yuskegoto/BluetoothDongleForTing/tingCode/OiDs/15001.png

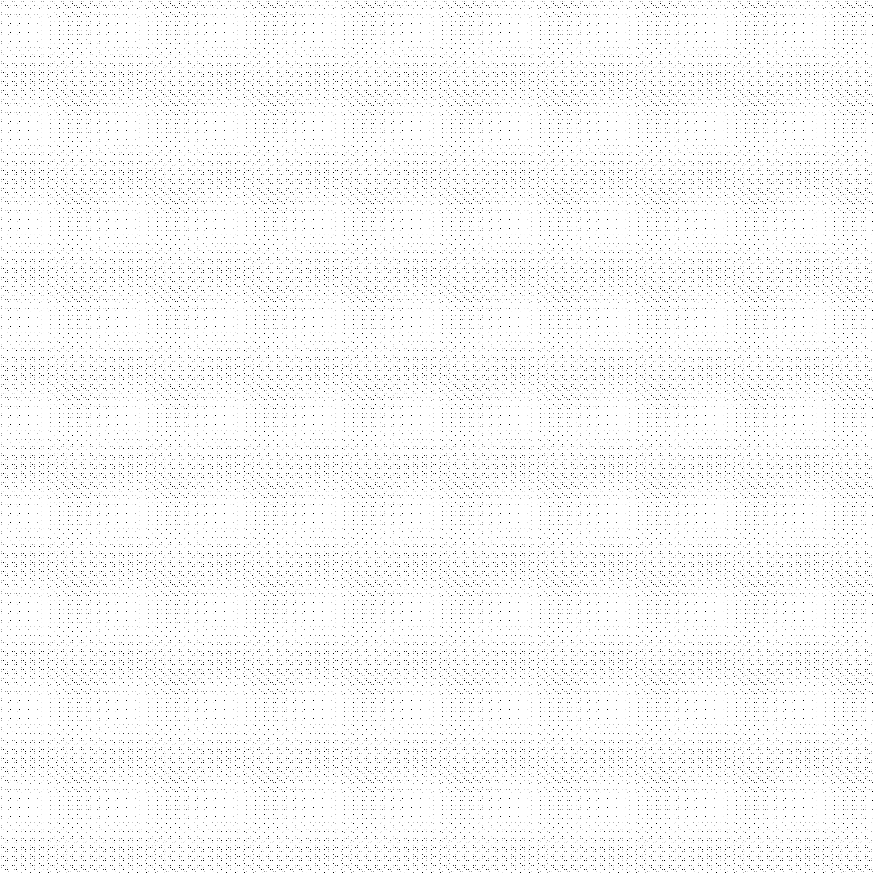
tingCode/OiDs/15001.png
