yuskegoto/BluetoothDongleForTing/tingCode/OiDs/15002.png

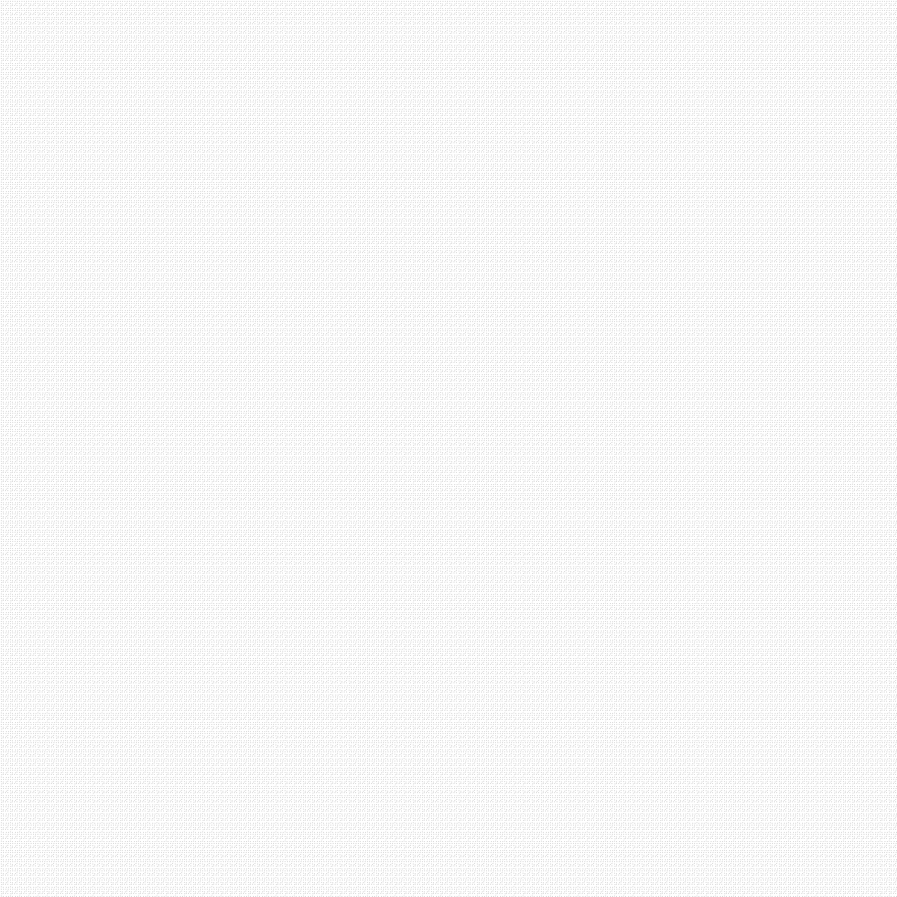
tingCode/OiDs/15002.png
