yuskegoto/BluetoothDongleForTing/tingCode/OiDs/15003.png

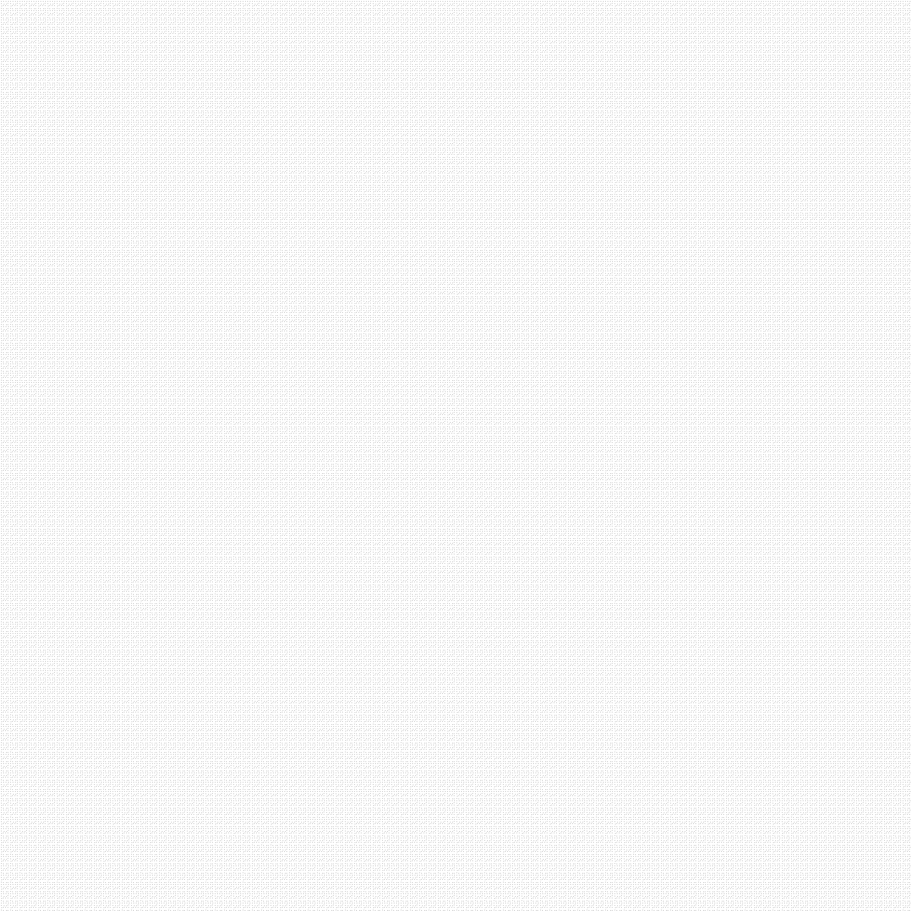
tingCode/OiDs/15003.png
